iotlibre/ecotherm/images/eco_measure.png

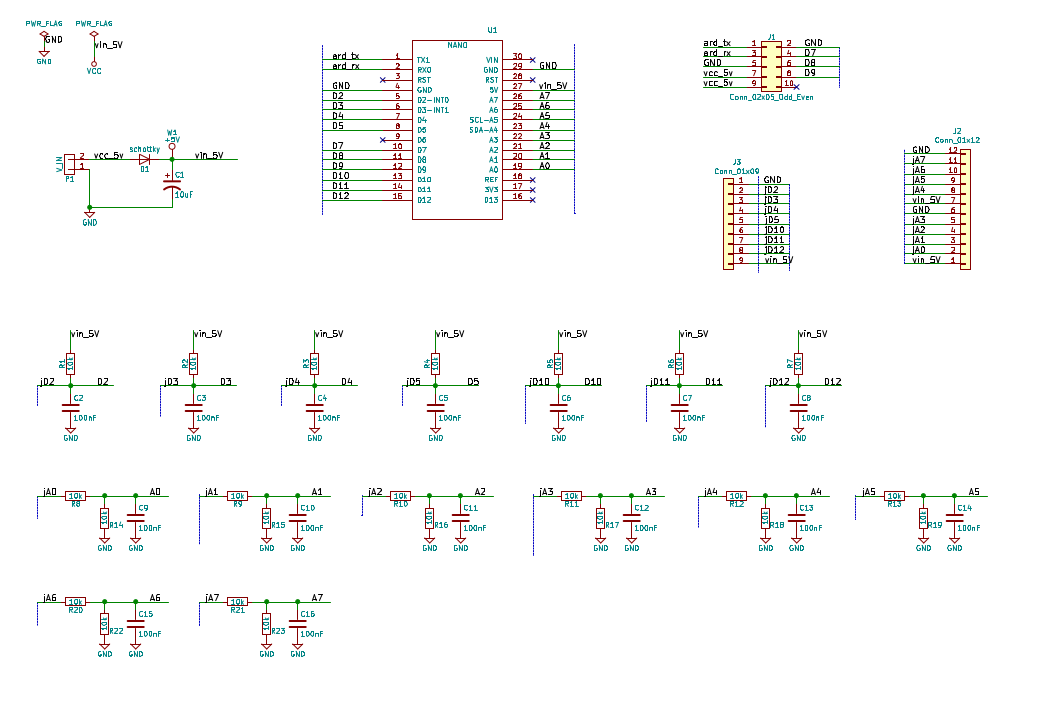
images/eco_measure.png
